cefali9154/BluetoothPlayer/Inc/BC127.h

/*
 * BC127.h
 *
 *  Created on: Jul 28, 2019
 *      Author: Matt
 */

#ifndef BC127_H_
#define BC127_H_

#include <stdint.h>

enum bc127Command_e{
	BLANK,
	PLAY,
	PAUSE,
	PAIR,
	PAIR_MODE,
	RESET_BC127
};

typedef enum {
	INIT_STATE,
	A2DP_OPEN,
	A2DP_CLOSED,
	CHARGING,
	CHARGED_FULL,
	NOT_CHARGING,
	INQUIRY_OK,
	PAIR_OK,
	PAIR_ERROR
}bc127Notification_e;

//extern bc127Notification_e Notification;

typedef enum {
	NOT_READY,
	READY,
	NOT_CONNECTED,
	CONNECTED,
	PLAYING,
	END_OF_FILE,
	NOT_PLAYING
}bc127Status_e;

//extern bc127Status_e Status;

typedef struct{
	char bluetoothAddress[12];
	uint8_t notification;
	uint8_t connectionStatus;
	uint8_t batteryStatus;
	uint8_t playStatus;
} bc127Device_t;

void bc127SendCommand(bc127Device_t *bc127, enum bc127Command_e command);
void bc127Read(bc127Device_t *bc127);
void bc127UartHandler(void);

#define DATA 1
#define NO_DATA 0

#endif /* BC127_H_ */
