cefali9154/BluetoothPlayer/Inc/Settings.h

/*
 * Settings.h
 *
 *  Created on: May 18, 2020
 *      Author: Matt
 */

#ifndef SETTINGS_H_
#define SETTINGS_H_

#define DEBUG

#define AUDIO_BUFFER_SIZE 512
#define DEBOUCE_TIME 50
#define AUTOCONN_TIMEOUT_MS 120000
#define PAIR_MODE_TIMEOUT_MS 30000
#define MAX_SONG_COUNT 128
//#define CONVERT_STEREO_TO_MONO

#endif /* SETTINGS_H_ */
