cefali9154/BluetoothPlayer/Src/globals.c

/*
 * globals.c
 *
 *  Created on: Jul 13, 2019
 *      Author: Matt
 */

#include "globals.h"

I2S_HandleTypeDef hi2s2;
DMA_HandleTypeDef hdma_spi2_tx;

DMA_HandleTypeDef huart2_rx;

SPI_HandleTypeDef hspi1;
DMA_HandleTypeDef hdma_spi1_rx;
DMA_HandleTypeDef hdma_spi1_tx;

TIM_HandleTypeDef htim2;
UART_HandleTypeDef huart1;
UART_HandleTypeDef huart2;


int _write(int file, char *data, int len)
{
   if ((file != STDOUT_FILENO) && (file != STDERR_FILENO))
   {
      errno = EBADF;
      return -1;
   }

   // arbitrary timeout 1000
   HAL_StatusTypeDef status =
      HAL_UART_Transmit(&huart1, (uint8_t*)data, len, 1000);

   // return # of bytes written - as best we can tell
   return (status == HAL_OK ? len : 0);
}
